nearestexit/t80-5000/documentation/5700.png

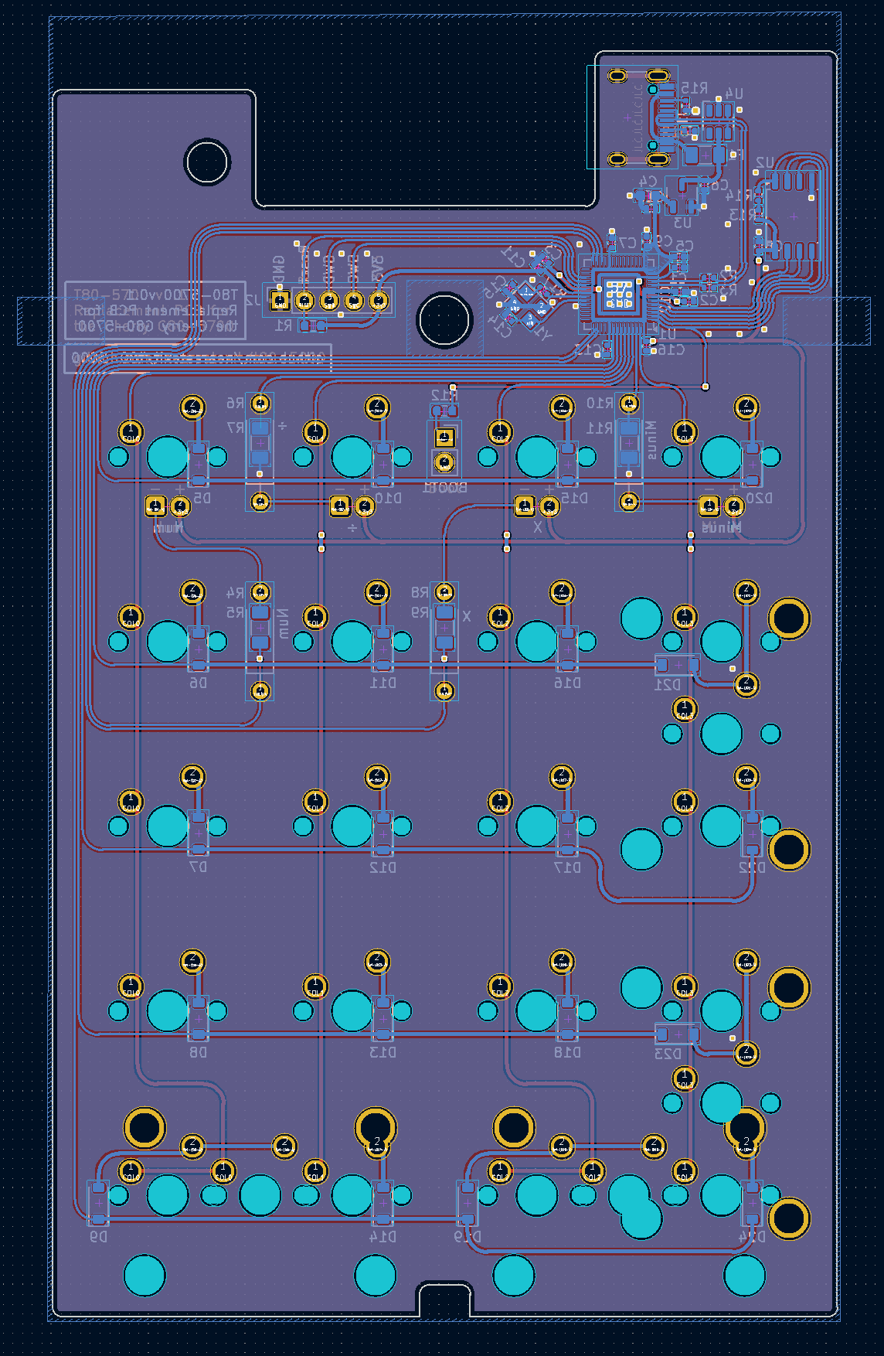
documentation/5700.png
